IanNNunez/ATENEA/AthenaTKL case/CASE/Plate.dxf

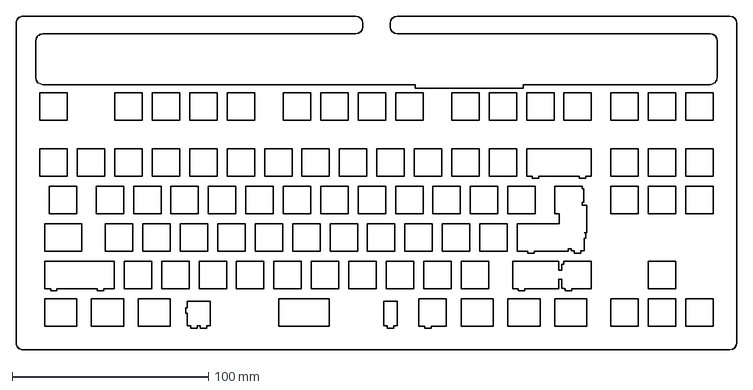
[picture p18: CAD file, 2021-06-03]
AthenaTKL case/CASE/Plate.dxf
366.7 x 169.7 mm
