IanNNunez/ATENEA/AteneaTKL-pcb/Graphics/Athenea wiring.png

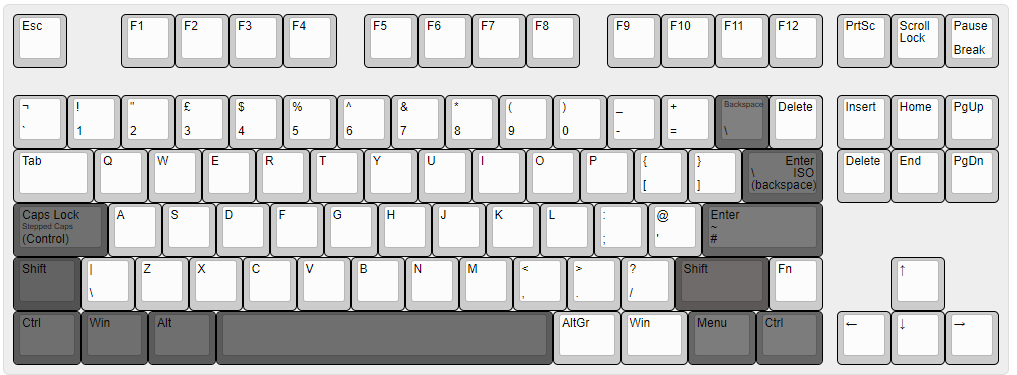
AteneaTKL-pcb/Graphics/Athenea wiring.png
